abichinger/dumbell_clamp/assets/signal-2023-01-07-223349_006.jpeg

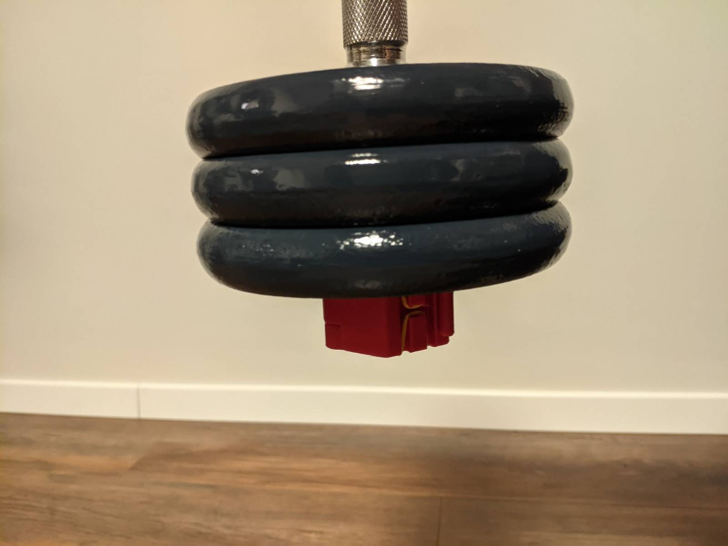
assets/signal-2023-01-07-223349_006.jpeg
